Unlegitbabo/retrophone/schema/schema.kicad_sch

## KiCad design schema/schema.kicad_sch (2026-06-08)

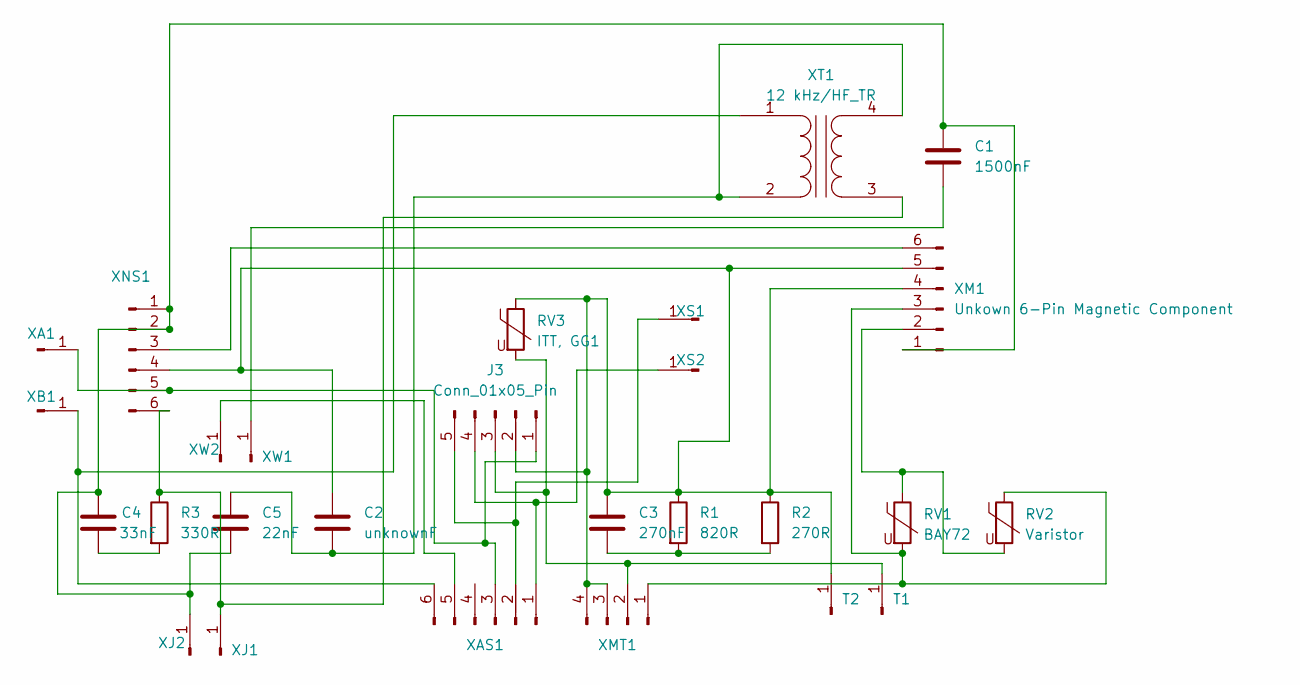
[picture p2: schematic schema.kicad_sch]

Parts:
C1: 1500nF
C2: unknownF
C3: 270nF
C4: 33nF
C5: 22nF
J3: Conn_01x05_Pin
R1: 820R
R2: 270R
R3: 330R
RV1: BAY72
RV2: Varistor
RV3: ITT, GG1
T1, T2: Conn_01x01_Pin
XA1: A
XAS1: Conn_01x06_Pin
XB1: Conn_01x01_Pin
XJ1, XJ2: Conn_01x01_Pin
XM1: Unkown 6-Pin Magnetic Component
XMT1: Conn_01x04_Pin
XNS1: Conn_01x06_Pin
XS1, XS2: Conn_01x01_Pin
XT1: 12 kHz/HF_TR
XW1, XW2: Conn_01x01_Pin

Connections:
unnamed: C1.1, C4.1, C5.2, XJ2.1, XM1.1, XNS1.1, XNS1.2
unnamed: C1.2, XW1.1
unnamed: C2.1, C3.1, J3.2, R1.1, R2.1, RV3.1, T2.1, XM1.4, XM1.5, XMT1.3, XMT1.4, XNS1.4
unnamed: C2.2, C5.1, XT1.2 (AB), XT1.4 (SB)
unnamed: C3.2, R1.2, R2.2
unnamed: C4.2, R3.2
unnamed: J3.1, XA1.1, XAS1.3, XNS1.5
unnamed: J3.3, RV3.2, T1.1, XMT1.2
unnamed: J3.4, XAS1.1, XS2.1
unnamed: J3.5, XAS1.2, XS1.1
unnamed: R3.1, XJ1.1, XNS1.6, XT1.3 (SA)
unnamed: RV1.1, RV2.2, XM1.2
unnamed: RV1.2, RV2.1, XM1.3, XMT1.1
unnamed: XAS1.5, XW2.1
unnamed: XAS1.6, XB1.1, XT1.1 (AA)
unnamed: XM1.6, XNS1.3
