Unlegitbabo/retrophone/schema/schema_esp32/schema_esp32.kicad_sch

## KiCad design schema/schema_esp32/schema_esp32.kicad_sch (2026-06-09, an earlier design)

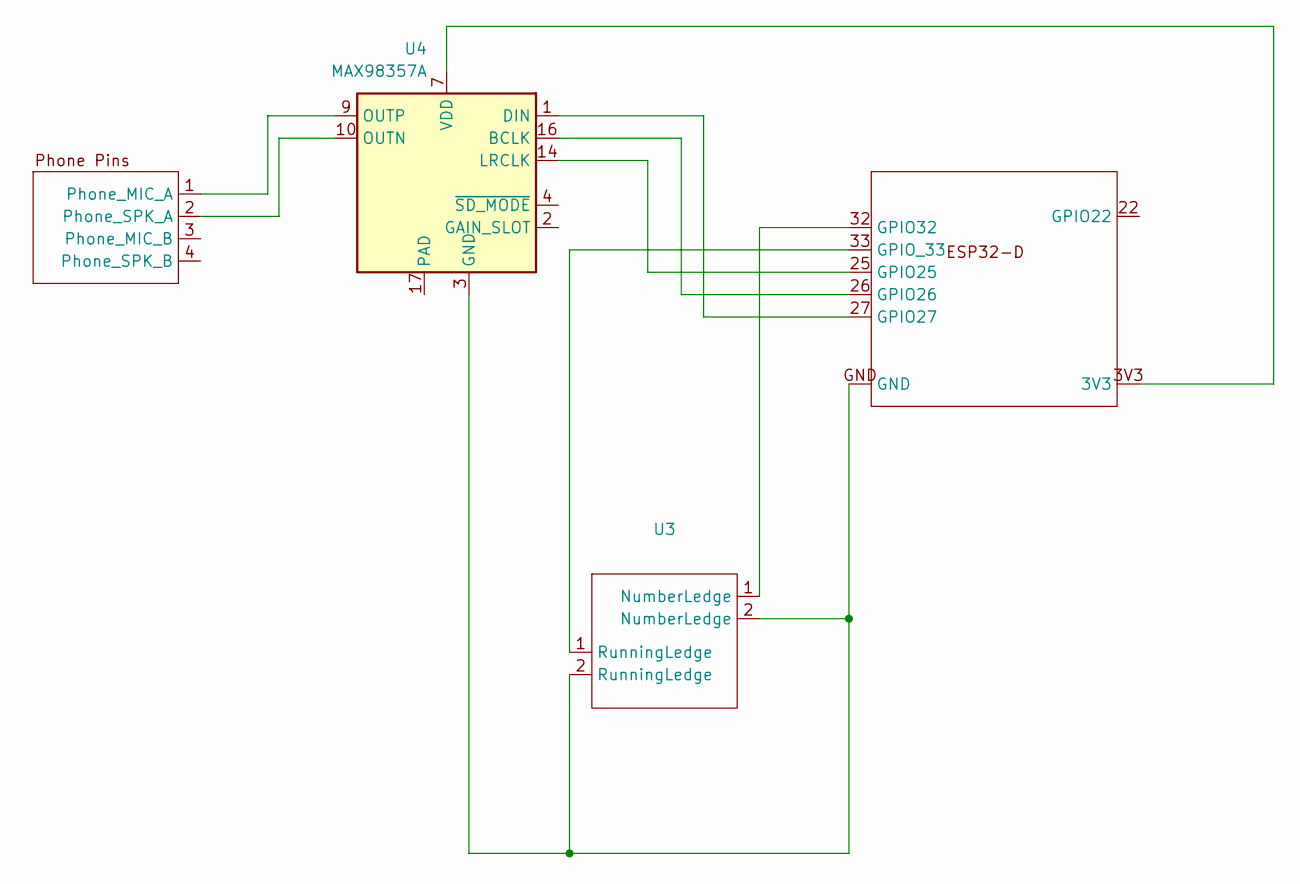
[picture p3: schematic schema_esp32.kicad_sch]

Parts:
U1, U2, U3: (no value)
U4: MAX98357A; TQFN-16-1EP_3x3mm_P0.5mm_EP1.23x1.23mm

Connections:
unnamed: U1.3V3, U4.7 (VDD), U4.8 (VDD)
unnamed: U1.25 (GPIO25), U4.14 (LRCLK)
unnamed: U1.26 (GPIO26), U4.16 (BCLK)
unnamed: U1.27 (GPIO27), U4.1 (DIN)
unnamed: U1.32 (GPIO32), U3.1
unnamed: U1.33 (GPIO_33), U3.1
unnamed: U1.GND, U3.2, U4.3 (GND), U4.11 (GND), U4.15 (GND)
unnamed: U2.1 (Phone_MIC_A), U4.9 (OUTP)
unnamed: U2.2 (Phone_SPK_A), U4.10 (OUTN)
