Unlegitbabo/retrophone/firmware/esp32dev/include/Debug.h

#pragma once
#include <Arduino.h>

#define DEBUG 0

#if DEBUG
  #define DEBUG_PRINT(x) Serial.print(x)
  #define DEBUG_PRINTLN(x) Serial.println(x)
#else
  #define DEBUG_PRINT(x)
  #define DEBUG_PRINTLN(x)
#endif
